SirioGuy/uClock/firmware/uClockArduino/display.h

#pragma once
#include "U8g2lib.h"
#include "Wire.h"

extern U8G2_SSD1306_128X64_NONAME_1_HW_I2C oled;

extern char secondChar[3];
extern char clockChar[9];

extern char timezoneChar[4];

extern float batteryLevel;

extern const char* TimeZoneNames[];

                                     //0x1ffc
const uint8_t battery_level_icon[] = {0xfc, 0x1f, 0x07, 0x10, 0x01, 0x10, 0x01, 0x10, 0x01, 0x10, 0x07, 0x10, 0xfc, 0x1f};
const uint8_t WiFi_indicator_icon[] = {0xf8, 0x00, 0x04, 0x01, 0x72, 0x02, 0x89, 0x04, 0x24, 0x01, 0x70, 0x00, 0x20, 0x00};
const uint8_t uClock_icon[] = { 
  0xc0,0x0b,0x00,0x00,
  0x20,0x88,0xe3,0x12,
  0x29,0x48,0x14,0x12,
  0x29,0x48,0x14,0x0a,
  0x29,0x48,0x14,0x0e,
  0x29,0x48,0x14,0x12,
  0xc7,0x93,0xe3,0x12,
  0x01,0x00,0x00,0x00 
}; 


// MAIN FUNCTION
void display();

void displayMargins();
void displayClock();
void displaySeconds();
void displayTimeZone();
void displayDate();

void displayBatteryLevel();
void displayWiFiActive();

void displayName();
